bml3mk5/L3S1VirtualFloppy/Software/Main/src/l3font.c

/**
 * @file l3font.c
 * @author Sasaji
 * @brief font data such like L3
 * @version 0.1
 * @date 2024-11-10
 * 
 * @copyright Copyright (c) Sasaji 2024
 * 
 */

#include "l3font.h"

const uint8_t l3font[256][16] = {
	{ 0x00,0x00,0x00,0x00,0x00,0x00,0x00,0x00, 0x00,0x00,0x00,0x00,0x00,0x00,0x00,0x00 },	/* 0x00 */
	{ 0x00,0xc0,0xc0,0xfc,0xf0,0xc0,0x00,0x00, 0x00,0x00,0x00,0x0f,0x03,0x00,0x00,0x00 },	/* 0x01 */
	{ 0x00,0xc0,0x00,0xc0,0x30,0x0c,0x00,0x00, 0x00,0x00,0x03,0x00,0x00,0x00,0x00,0x00 },	/* 0x02 */
	{ 0x00,0x0c,0x30,0xc0,0x30,0x0c,0x00,0x00, 0x00,0x0c,0x03,0x00,0x03,0x0c,0x00,0x00 },	/* 0x03 */
	{ 0x00,0x00,0xfc,0xf0,0xc0,0x00,0x00,0x00, 0x00,0x00,0x0f,0x03,0x00,0x00,0x00,0x00 },	/* 0x04 */
	{ 0x00,0xf0,0xfc,0xfc,0xfc,0xf0,0x00,0x00, 0x00,0x03,0x0f,0x0f,0x0f,0x03,0x00,0x00 },	/* 0x05 */
	{ 0x00,0xfc,0xfc,0xfc,0xfc,0xfc,0x00,0x00, 0x00,0x0f,0x0f,0x0f,0x0f,0x0f,0x00,0x00 },	/* 0x06 */
	{ 0x00,0xfc,0xfc,0x00,0xfc,0xfc,0x00,0x00, 0x00,0x0f,0x0f,0x00,0x0f,0x0f,0x00,0x00 },	/* 0x07 */
	{ 0xff,0xc3,0xc3,0x3c,0x00,0x00,0xc0,0xc0, 0x3f,0x30,0x30,0x0f,0x00,0xc3,0xcc,0x30 },	/* 0x08 */
	{ 0xff,0xc0,0xc0,0xff,0x00,0xc0,0xc0,0xc0, 0x3f,0x00,0x00,0x3f,0x00,0x00,0xff,0x00 },	/* 0x09 */
	{ 0xff,0x00,0x00,0x00,0x00,0xc0,0xc0,0xc0, 0x3f,0x30,0x30,0x30,0x00,0xff,0x0c,0x0c },	/* 0x0a */
	{ 0xff,0xc0,0xc0,0xff,0x00,0xc0,0x00,0xc0, 0x3f,0x00,0x00,0x3f,0x00,0xff,0x0f,0xff },	/* 0x0b */
	{ 0xfc,0x03,0x03,0x0c,0x00,0xc0,0x00,0x00, 0x0f,0x30,0x30,0x0c,0x00,0xff,0xc0,0xc0 },	/* 0x0c */
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
	{ 0x00,0x3c,0xc3,0xc3,0x3c,0x00,0x00,0x00, 0x00,0x0f,0x30,0x30,0x33,0x0c,0x33,0x00 },	/* 0x26 */
	{ 0x00,0x00,0x00,0x30,0x0f,0x00,0x00,0x00, 0x00,0x00,0x00,0x00,0x00,0x00,0x00,0x00 },	/* 0x27 */
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
};
