bml3mk5/L3S1VirtualFloppy/Software/Main/src/display.h

/**
 * @file display.h
 * @author Sasaji
 * @brief 
 * @version 0.1
 * @date 2024-10-18
 * 
 * @copyright Copyright (c) Sasaji 2024
 * 
 */

#ifndef DISPLAY_H
#define DISPLAY_H

#include <stdint.h>
#include <stdbool.h>
#include <string.h>
#include "i2c_lcd_1602.h"
#include "i2c_ssd1306.h"
#include "i2c_led_btn.h"
#include "simple_list.h"

//#define RCURSOR '>'
#define RCURSOR 0x01

enum en_display_phase {
    PHASE_STORAGE = 0,
    PHASE_MENU,
    PHASE_SETTING,
    PHASE_RESET,
    PHASE_MESSAGE,
};

typedef struct st_display_info {
    int phase;
} display_info_t;

typedef struct st_display_pos {
    int16_t c;
    int16_t n;
} display_pos_t;

extern i2c_lcd_1602_t   i2c_lcd;
extern i2c_ssd1306_t    i2c_oled;
extern i2c_led_btn_t    i2c_led_btn;

extern display_info_t   display_info;

void display_init(void);
void display_task(void);
void display_busy_task(void);

void display_reset_i2c_display(void);

int16_t display_change_choice(int dir, int16_t pos, size_t count);

#define FILE_TITLE_SIZE 40

typedef struct st_text_shift {
    int phase;
    int pos;
    int pos_max;
    uint32_t ms;
    char text[FILE_TITLE_SIZE + 1];
} text_shift_t;

void text_shift_init(text_shift_t *text);
void text_shift_set(text_shift_t *text, const char *n_str, size_t n_len);
void text_shift_task(text_shift_t *text);

void display_config_make_path(int img_drv, const char *file_name, simple_list_t *tree);
void display_config_set_path(int img_drv, const char *file_path, uint8_t side_number);
void display_config_clear_path(int img_drv);
void display_config_set_side_number(int img_drv, uint8_t side_number);

void display_led_state(int state);
//void display_led_state_immediately(int state);
void display_led_force(uint8_t data, uint8_t mask);
void display_buzzer(void);

void display_progress(void);

void display_lcd_change_phase(void);

// wrapper of i2c_lcd_1602

void lcd_locate(int x, int y);
void lcd_char(char c);
void lcd_charset(char c, size_t len);
void lcd_string(const char *s);
void lcd_locate_char(int x, int y, char c);
void lcd_locate_charset(int x, int y, char c, size_t len);
void lcd_locate_string(int x, int y, const char *s);
void lcd_locate_substring(int x, int y, const char *s, size_t len);
void lcd_digit(int val);

/// @brief 
/// @param s : string
/// @param len : string length
/// @param size : padding size of string
static inline void lcd_padding(char *s, size_t len, size_t size)
{
    if (size > len) {
        memset(&s[len], 0x20, size - len);
    }
    s[size]=0;
}

#endif /* DISPLAY_H */
